MooDongLee/PNU_3D_Printing_Competition/Pictures/3.jpg

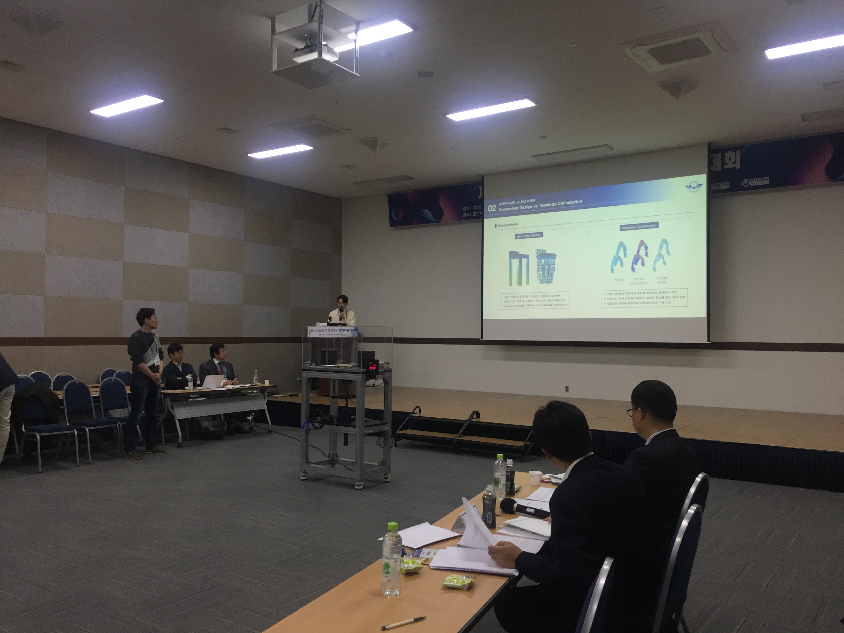
Pictures/3.jpg
